unipartdigital/tail/firmware/src/battery.h

/* battery.h */

#ifndef _BATTERY_H
#define _BATTERY_H

#include <stdint.h>
#include <stdbool.h>

void battery_init(bool allow_flat);
uint16_t battery_read(void);
int battery_state(uint16_t voltage);
int battery_mv(uint16_t voltage);
bool battery_flat(uint16_t voltage);

#endif /* _BATTERY_H */
